CXBRexDevs/Codigos-ejemplo-CXB/images/2023-07-07-10-22-03-image.png

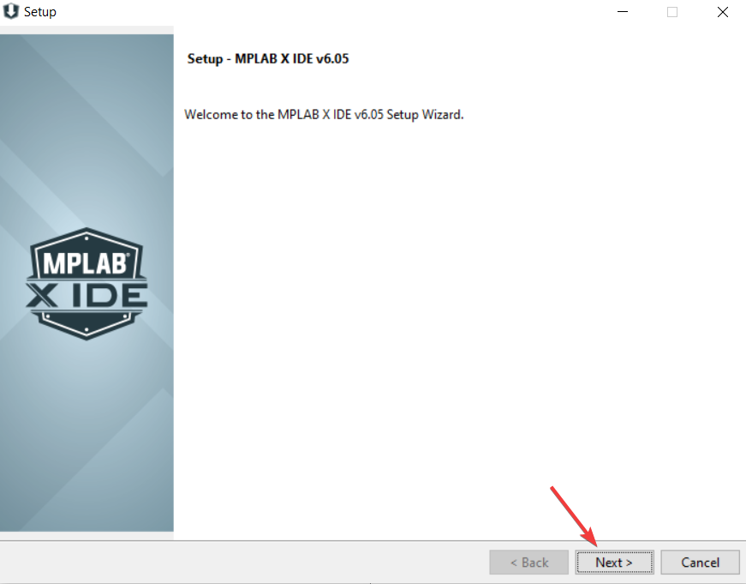
images/2023-07-07-10-22-03-image.png
