CXBRexDevs/Codigos-ejemplo-CXB/images/2023-07-07-10-25-39-image.png

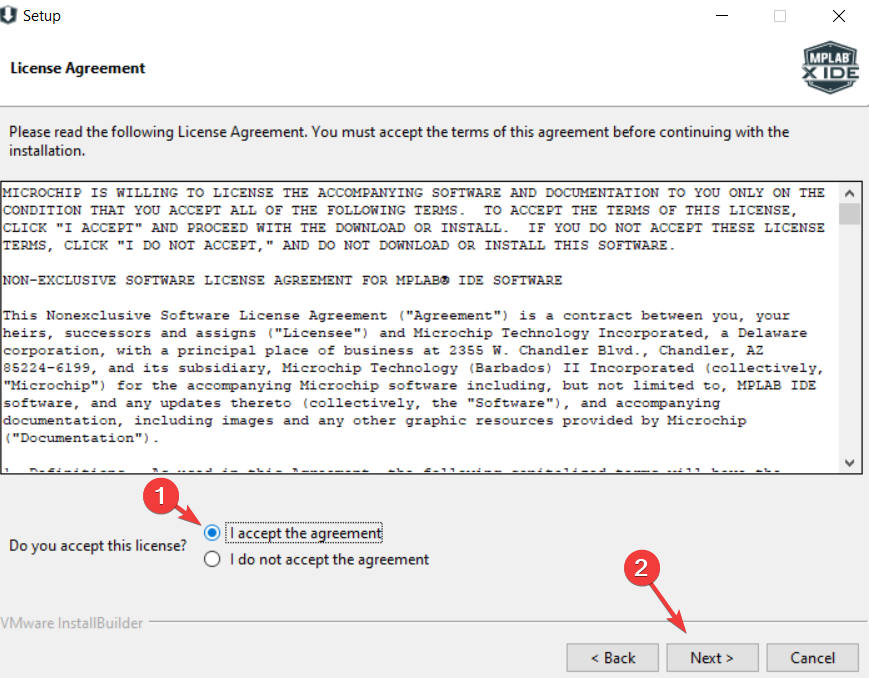
images/2023-07-07-10-25-39-image.png
