CXBRexDevs/Codigos-ejemplo-CXB/images/Codigo_ADC_1.png

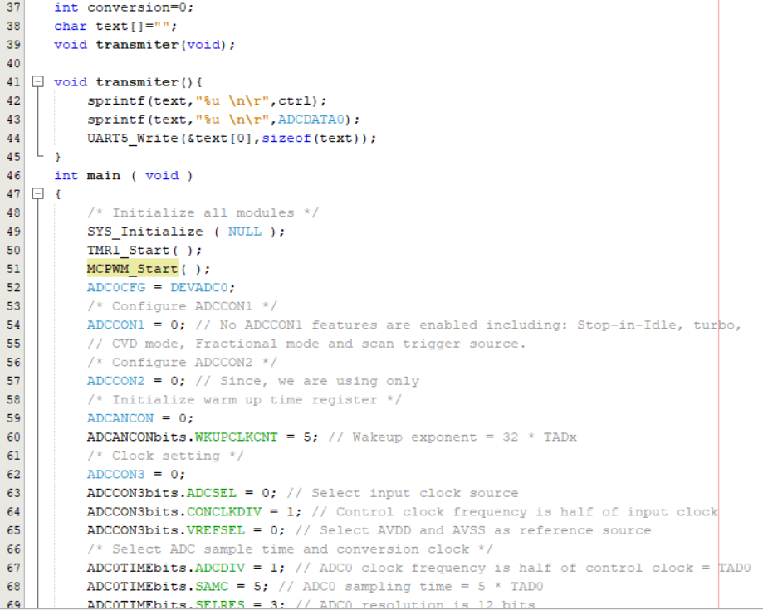
images/Codigo_ADC_1.png
