CXBRexDevs/Codigos-ejemplo-CXB/images/Codigo_ADC_2.png

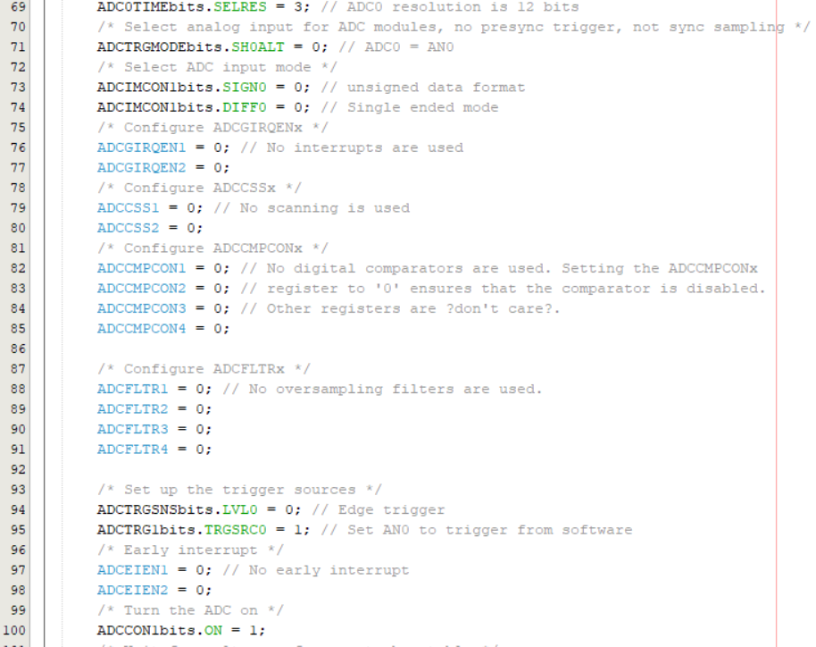
images/Codigo_ADC_2.png
