CXBRexDevs/Codigos-ejemplo-CXB/images/Codigo_ADC_3.png

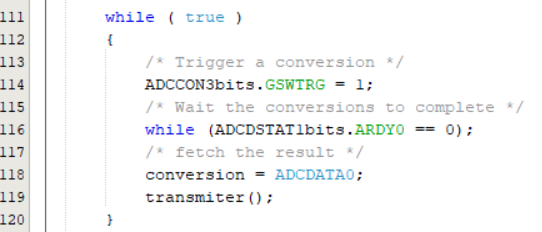
images/Codigo_ADC_3.png
