CXBRexDevs/Codigos-ejemplo-CXB/images/Main_PWM.png

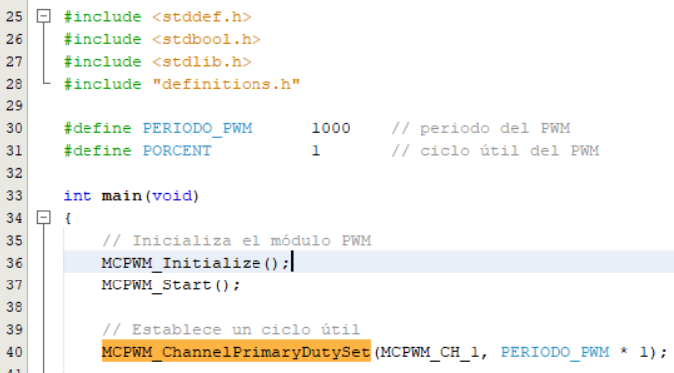
images/Main_PWM.png
