CXBRexDevs/Codigos-ejemplo-CXB/images/SPI3.png

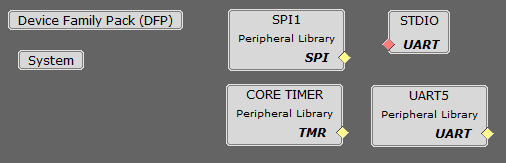
images/SPI3.png
