CXBRexDevs/Codigos-ejemplo-CXB/images/SPI4.png

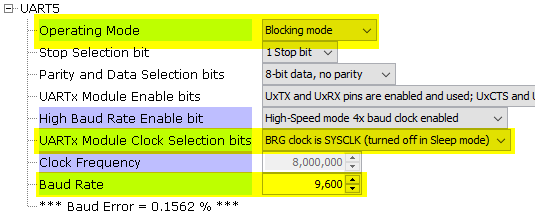
images/SPI4.png
