CXBRexDevs/Codigos-ejemplo-CXB/images/SPI5.png

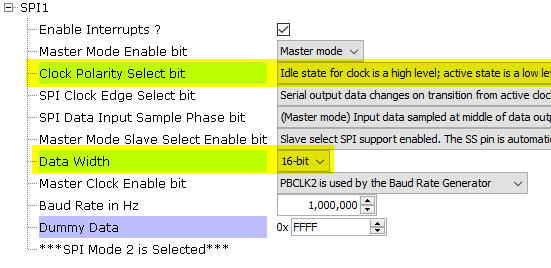
images/SPI5.png
