CXBRexDevs/Codigos-ejemplo-CXB/images/SPI6.png

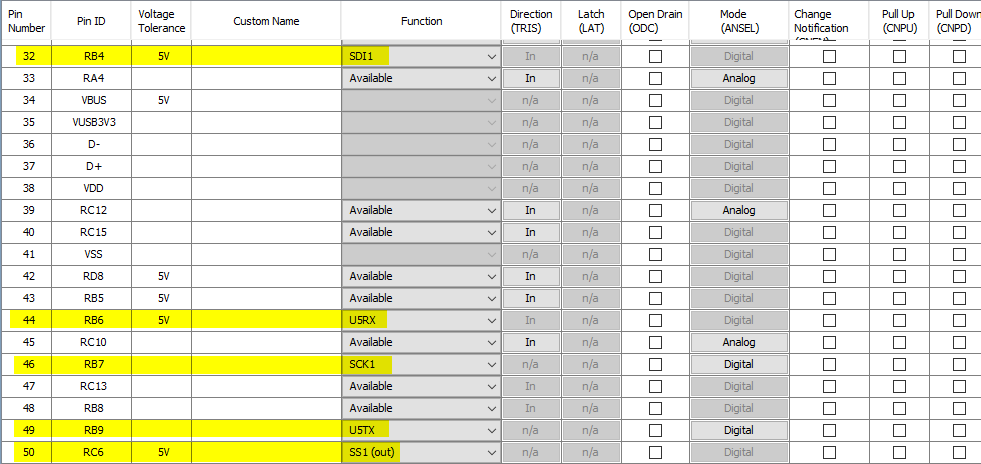
images/SPI6.png
