CXBRexDevs/Codigos-ejemplo-CXB/images/SPI7.png

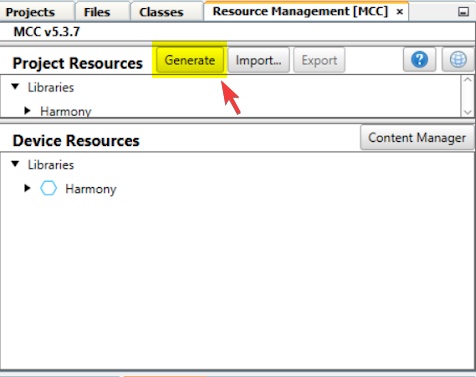
images/SPI7.png
