CXBRexDevs/Codigos-ejemplo-CXB/images/SPI8.png

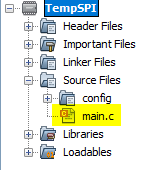
images/SPI8.png
