CXBRexDevs/Codigos-ejemplo-CXB/images/SPI9.png

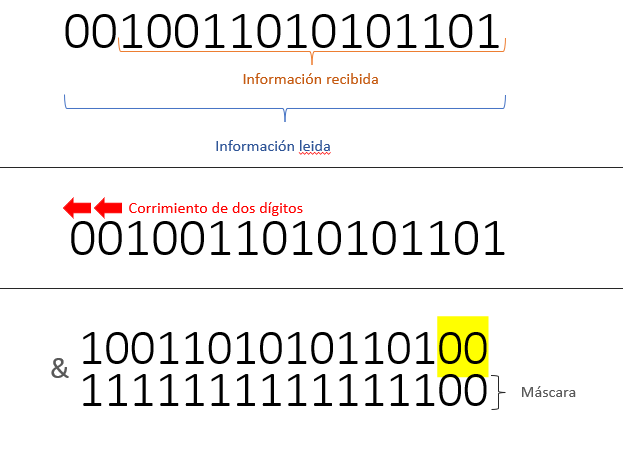
images/SPI9.png
