CXBRexDevs/Codigos-ejemplo-CXB/images/SPI10.png

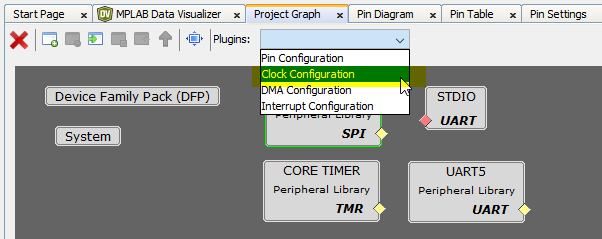
images/SPI10.png
