CXBRexDevs/Codigos-ejemplo-CXB/images/SPI11.png

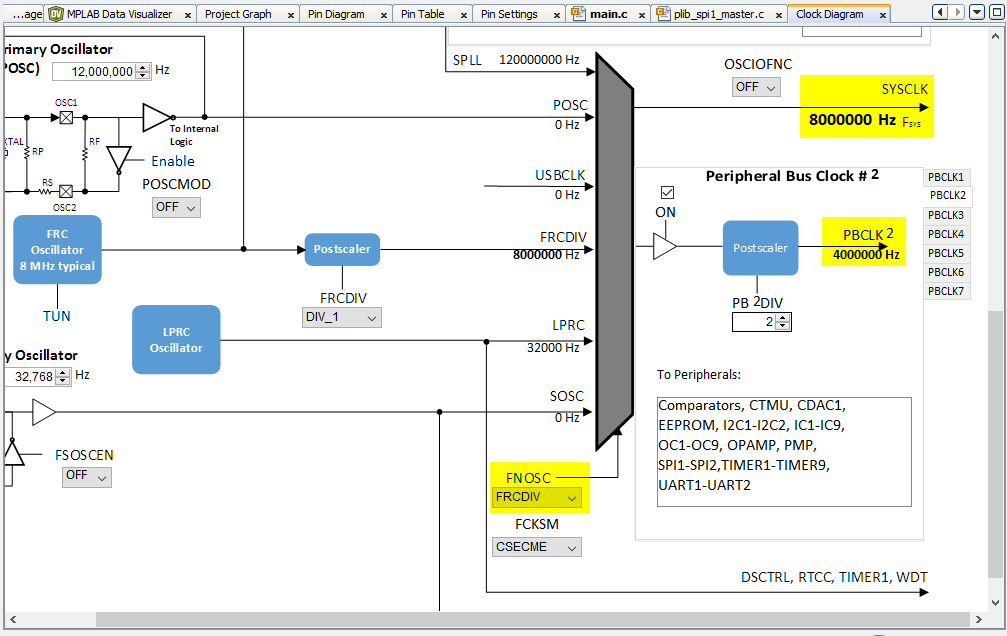
images/SPI11.png
