CXBRexDevs/Codigos-ejemplo-CXB/CXB_Rex_Periferals/firmware/src/config/default_PIC32MK1024MCF064/initialization.c

/*******************************************************************************
  System Initialization File

  File Name:
    initialization.c

  Summary:
    This file contains source code necessary to initialize the system.

  Description:
    This file contains source code necessary to initialize the system.  It
    implements the "SYS_Initialize" function, defines the configuration bits,
    and allocates any necessary global system resources,
 *******************************************************************************/

// DOM-IGNORE-BEGIN
/*******************************************************************************
* Copyright (C) 2018 Microchip Technology Inc. and its subsidiaries.
*
* Subject to your compliance with these terms, you may use Microchip software
* and any derivatives exclusively with Microchip products. It is your
* responsibility to comply with third party license terms applicable to your
* use of third party software (including open source software) that may
* accompany Microchip software.
*
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
* IN NO EVENT WILL MICROCHIP BE LIABLE FOR ANY INDIRECT, SPECIAL, PUNITIVE,
* INCIDENTAL OR CONSEQUENTIAL LOSS, DAMAGE, COST OR EXPENSE OF ANY KIND
* WHATSOEVER RELATED TO THE SOFTWARE, HOWEVER CAUSED, EVEN IF MICROCHIP HAS
* BEEN ADVISED OF THE POSSIBILITY OR THE DAMAGES ARE FORESEEABLE. TO THE
* FULLEST EXTENT ALLOWED BY LAW, MICROCHIP'S TOTAL LIABILITY ON ALL CLAIMS IN
* ANY WAY RELATED TO THIS SOFTWARE WILL NOT EXCEED THE AMOUNT OF FEES, IF ANY,
* THAT YOU HAVE PAID DIRECTLY TO MICROCHIP FOR THIS SOFTWARE.
 *******************************************************************************/
// DOM-IGNORE-END

// *****************************************************************************
// *****************************************************************************
// Section: Included Files
// *****************************************************************************
// *****************************************************************************
#include "definitions.h"
#include "device.h"


// ****************************************************************************
// ****************************************************************************
// Section: Configuration Bits
// ****************************************************************************
// ****************************************************************************

/*** DEVCFG0 ***/
#pragma config DEBUG =      OFF
#pragma config JTAGEN =     OFF
#pragma config ICESEL =     ICS_PGx1
#pragma config TRCEN =      OFF
#pragma config BOOTISA =    MIPS32
#pragma config FSLEEP =     OFF
#pragma config DBGPER =     PG_ALL
#pragma config SMCLR =      MCLR_NORM
#pragma config SOSCGAIN =   GAIN_2X
#pragma config SOSCBOOST =  ON
#pragma config POSCGAIN =   GAIN_LEVEL_3
#pragma config POSCBOOST =  ON
#pragma config EJTAGBEN =   NORMAL

/*** DEVCFG1 ***/
#pragma config FNOSC =      SPLL
#pragma config DMTINTV =    WIN_127_128
#pragma config FSOSCEN =    OFF
#pragma config IESO =       ON
#pragma config POSCMOD =    OFF
#pragma config OSCIOFNC =   OFF
#pragma config FCKSM =      CSECME
#pragma config WDTPS =      PS1048576
#pragma config WDTSPGM =    STOP
#pragma config FWDTEN =     OFF
#pragma config WINDIS =     NORMAL
#pragma config FWDTWINSZ =  WINSZ_25
#pragma config DMTCNT =     DMT31
#pragma config FDMTEN =     OFF

/*** DEVCFG2 ***/
#pragma config FPLLIDIV =   DIV_1
#pragma config FPLLRNG =    RANGE_5_10_MHZ
#pragma config FPLLICLK =   PLL_FRC
#pragma config FPLLMULT =   MUL_60
#pragma config FPLLODIV =   DIV_4
#pragma config VBATBOREN =  ON
#pragma config DSBOREN =    ON
#pragma config DSWDTPS =    DSPS32
#pragma config DSWDTOSC =   LPRC
#pragma config DSWDTEN =    OFF
#pragma config FDSEN =      ON
#pragma config BORSEL =     HIGH
#pragma config UPLLEN =     OFF

/*** DEVCFG3 ***/
#pragma config USERID =     0xffff
#pragma config FUSBIDIO2 =   ON
#pragma config FVBUSIO2 =  ON
#pragma config PGL1WAY =    ON
#pragma config PMDL1WAY =   ON
#pragma config IOL1WAY =    ON
#pragma config FUSBIDIO1 =   ON
#pragma config FVBUSIO1 =  ON
#pragma config PWMLOCK =  OFF

/*** BF1SEQ ***/
#pragma config TSEQ =       0x0
#pragma config CSEQ =       0xffff





// *****************************************************************************
// *****************************************************************************
// Section: Driver Initialization Data
// *****************************************************************************
// *****************************************************************************
/* Following MISRA-C rules are deviated in the below code block */
/* MISRA C-2012 Rule 11.1 */
/* MISRA C-2012 Rule 11.3 */
/* MISRA C-2012 Rule 11.8 */



// *****************************************************************************
// *****************************************************************************
// Section: System Data
// *****************************************************************************
// *****************************************************************************

// *****************************************************************************
// *****************************************************************************
// Section: Library/Stack Initialization Data
// *****************************************************************************
// *****************************************************************************


// *****************************************************************************
// *****************************************************************************
// Section: System Initialization
// *****************************************************************************
// *****************************************************************************



// *****************************************************************************
// *****************************************************************************
// Section: Local initialization functions
// *****************************************************************************
// *****************************************************************************

/*******************************************************************************
  Function:
    void STDIO_BufferModeSet ( void )

  Summary:
    Sets the buffering mode for stdin and stdout

  Remarks:
 ********************************************************************************/
static void STDIO_BufferModeSet(void)
{
    /* MISRAC 2012 deviation block start */
    /* MISRA C-2012 Rule 21.6 deviated 2 times in this file.  Deviation record ID -  H3_MISRAC_2012_R_21_6_DR_3 */

    /* Make stdin unbuffered */
    setbuf(stdin, NULL);

    /* Make stdout unbuffered */
    setbuf(stdout, NULL);
}


/* MISRAC 2012 deviation block end */

/*******************************************************************************
  Function:
    void SYS_Initialize ( void *data )

  Summary:
    Initializes the board, services, drivers, application and other modules.

  Remarks:
 */

void SYS_Initialize ( void* data )
{

    /* MISRAC 2012 deviation block start */
    /* MISRA C-2012 Rule 2.2 deviated in this file.  Deviation record ID -  H3_MISRAC_2012_R_2_2_DR_1 */

    /* Start out with interrupts disabled before configuring any modules */
    (void)__builtin_disable_interrupts();

    STDIO_BufferModeSet();


  
    CLK_Initialize();

    /* Configure CP0.K0 for optimal performance (cached instruction pre-fetch) */
    __builtin_mtc0(16, 0,(__builtin_mfc0(16, 0) | 0x3U));

    /* Configure Wait States and Prefetch */
    CHECONbits.PFMWS = 3;
    CHECONbits.PREFEN = 0;



	GPIO_Initialize();

    CORETIMER_Initialize();
    ADCHS_Initialize();

    QEI1_Initialize();

    CAN1_Initialize();

    TMR1_Initialize();

    MCPWM_Initialize();

	SPI1_Initialize();

	UART5_Initialize();

	UART6_Initialize();



    /* MISRAC 2012 deviation block start */
    /* Following MISRA-C rules deviated in this block  */
    /* MISRA C-2012 Rule 11.3 - Deviation record ID - H3_MISRAC_2012_R_11_3_DR_1 */
    /* MISRA C-2012 Rule 11.8 - Deviation record ID - H3_MISRAC_2012_R_11_8_DR_1 */




    /* MISRAC 2012 deviation block end */
    EVIC_Initialize();

	/* Enable global interrupts */
    (void)__builtin_enable_interrupts();



    /* MISRAC 2012 deviation block end */
}

/*******************************************************************************
 End of File
*/
