CXBRexDevs/Codigos-ejemplo-CXB/CXB_Rex_Periferals/firmware/src/config/default_PIC32MK1024MCF064/peripheral/gpio/plib_gpio.c

/*******************************************************************************
  SYS PORTS Static Functions for PORTS System Service

  Company:
    Microchip Technology Inc.

  File Name:
    plib_gpio.c

  Summary:
    GPIO function implementations for the GPIO PLIB.

  Description:
    The GPIO PLIB provides a simple interface to manage peripheral
    input-output controller.

*******************************************************************************/

//DOM-IGNORE-BEGIN
/*******************************************************************************
* Copyright (C) 2019 Microchip Technology Inc. and its subsidiaries.
*
* Subject to your compliance with these terms, you may use Microchip software
* and any derivatives exclusively with Microchip products. It is your
* responsibility to comply with third party license terms applicable to your
* use of third party software (including open source software) that may
* accompany Microchip software.
*
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
* IN NO EVENT WILL MICROCHIP BE LIABLE FOR ANY INDIRECT, SPECIAL, PUNITIVE,
* INCIDENTAL OR CONSEQUENTIAL LOSS, DAMAGE, COST OR EXPENSE OF ANY KIND
* WHATSOEVER RELATED TO THE SOFTWARE, HOWEVER CAUSED, EVEN IF MICROCHIP HAS
* BEEN ADVISED OF THE POSSIBILITY OR THE DAMAGES ARE FORESEEABLE. TO THE
* FULLEST EXTENT ALLOWED BY LAW, MICROCHIP'S TOTAL LIABILITY ON ALL CLAIMS IN
* ANY WAY RELATED TO THIS SOFTWARE WILL NOT EXCEED THE AMOUNT OF FEES, IF ANY,
* THAT YOU HAVE PAID DIRECTLY TO MICROCHIP FOR THIS SOFTWARE.
*******************************************************************************/
//DOM-IGNORE-END

#include "plib_gpio.h"
#include "interrupts.h"




/******************************************************************************
  Function:
    GPIO_Initialize ( void )

  Summary:
    Initialize the GPIO library.

  Remarks:
    See plib_gpio.h for more details.
*/
void GPIO_Initialize ( void )
{

    /* PORTA Initialization */
    LATA = 0x0U; /* Initial Latch Value */
    TRISACLR = 0x1800U; /* Direction Control */
    ANSELACLR = 0x1800U; /* Digital Mode Enable */
    /* PORTB Initialization */
    ANSELBCLR = 0x280U; /* Digital Mode Enable */
    /* PORTC Initialization */
    ANSELCCLR = 0x400U; /* Digital Mode Enable */
    /* PORTD Initialization */
    /* PORTE Initialization */
    /* PORTF Initialization */
    /* PORTG Initialization */

    /* Unlock system for PPS configuration */
    SYSKEY = 0x00000000U;
    SYSKEY = 0xAA996655U;
    SYSKEY = 0x556699AAU;

    CFGCONbits.IOLOCK = 0U;

    /* PPS Input Remapping */
    SDI1R = 2;
    QEA1R = 5;
    U5RXR = 0;
    U4RXR = 9;
    C1RXR = 12;
    QEB1R = 6;

    /* PPS Output Remapping */
    RPB5R = 2;
    RPB9R = 11;
    RPF1R = 12;
    RPC6R = 3;

        /* Lock back the system after PPS configuration */
    CFGCONbits.IOLOCK = 1U;

    SYSKEY = 0x00000000U;

}

// *****************************************************************************
// *****************************************************************************
// Section: GPIO APIs which operates on multiple pins of a port
// *****************************************************************************
// *****************************************************************************

// *****************************************************************************
/* Function:
    uint32_t GPIO_PortRead ( GPIO_PORT port )

  Summary:
    Read all the I/O lines of the selected port.

  Description:
    This function reads the live data values on all the I/O lines of the
    selected port.  Bit values returned in each position indicate corresponding
    pin levels.
    1 = Pin is high.
    0 = Pin is low.

    This function reads the value regardless of pin configuration, whether it is
    set as as an input, driven by the GPIO Controller, or driven by a peripheral.

  Remarks:
    If the port has less than 32-bits, unimplemented pins will read as
    low (0).
    Implemented pins are Right aligned in the 32-bit return value.
*/
uint32_t GPIO_PortRead(GPIO_PORT port)
{
    return (*(volatile uint32_t *)(&PORTA + (port * 0x40U)));
}

// *****************************************************************************
/* Function:
    void GPIO_PortWrite (GPIO_PORT port, uint32_t mask, uint32_t value);

  Summary:
    Write the value on the masked I/O lines of the selected port.

  Remarks:
    See plib_gpio.h for more details.
*/
void GPIO_PortWrite(GPIO_PORT port, uint32_t mask, uint32_t value)
{
    *(volatile uint32_t *)(&LATA + (port * 0x40U)) = (*(volatile uint32_t *)(&LATA + (port * 0x40U)) & (~mask)) | (mask & value);
}

// *****************************************************************************
/* Function:
    uint32_t GPIO_PortLatchRead ( GPIO_PORT port )

  Summary:
    Read the latched value on all the I/O lines of the selected port.

  Remarks:
    See plib_gpio.h for more details.
*/
uint32_t GPIO_PortLatchRead(GPIO_PORT port)
{
    return (*(volatile uint32_t *)(&LATA + (port * 0x40U)));
}

// *****************************************************************************
/* Function:
    void GPIO_PortSet ( GPIO_PORT port, uint32_t mask )

  Summary:
    Set the selected IO pins of a port.

  Remarks:
    See plib_gpio.h for more details.
*/
void GPIO_PortSet(GPIO_PORT port, uint32_t mask)
{
    *(volatile uint32_t *)(&LATASET + (port * 0x40U)) = mask;
}

// *****************************************************************************
/* Function:
    void GPIO_PortClear ( GPIO_PORT port, uint32_t mask )

  Summary:
    Clear the selected IO pins of a port.

  Remarks:
    See plib_gpio.h for more details.
*/
void GPIO_PortClear(GPIO_PORT port, uint32_t mask)
{
    *(volatile uint32_t *)(&LATACLR + (port * 0x40U)) = mask;
}

// *****************************************************************************
/* Function:
    void GPIO_PortToggle ( GPIO_PORT port, uint32_t mask )

  Summary:
    Toggles the selected IO pins of a port.

  Remarks:
    See plib_gpio.h for more details.
*/
void GPIO_PortToggle(GPIO_PORT port, uint32_t mask)
{
    *(volatile uint32_t *)(&LATAINV + (port * 0x40U))= mask;
}

// *****************************************************************************
/* Function:
    void GPIO_PortInputEnable ( GPIO_PORT port, uint32_t mask )

  Summary:
    Enables selected IO pins of a port as input.

  Remarks:
    See plib_gpio.h for more details.
*/
void GPIO_PortInputEnable(GPIO_PORT port, uint32_t mask)
{
    *(volatile uint32_t *)(&TRISASET + (port * 0x40U)) = mask;
}

// *****************************************************************************
/* Function:
    void GPIO_PortOutputEnable ( GPIO_PORT port, uint32_t mask )

  Summary:
    Enables selected IO pins of a port as output(s).

  Remarks:
    See plib_gpio.h for more details.
*/
void GPIO_PortOutputEnable(GPIO_PORT port, uint32_t mask)
{
    *(volatile uint32_t *)(&TRISACLR + (port * 0x40U)) = mask;
}




/*******************************************************************************
 End of File
*/
